asterix24/svaroskey/firmware/svaroskey/hw/hw_sipo.h

/**
 * \file
 * <!--
 * This file is part of BeRTOS.
 *
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
 * As a special exception, you may use this file as part of a free software
 * library without restriction.  Specifically, if other files instantiate
 * templates or use macros or inline functions from this file, or you compile
 * this file and link it with other files to produce an executable, this
 * file does not by itself cause the resulting executable to be covered by
 * the GNU General Public License.  This exception does not however
 * invalidate any other reasons why the executable file might be covered by
 * the GNU General Public License.
 *
 * Copyright 2003, 2004, 2006, 2008, 2009 Develer S.r.l. (http://www.develer.com/)
 * Copyright 2000 Bernie Innocenti <bernie@codewiz.org>
 * All Rights Reserved.
 * -->
 *
 * \brief Macro for HW_SIPO_H
 *
 *
 *
 * \author Andrea Grandi <andrea@develer.com>
 * \author Daniele Basile <asterix@develer.com>
 */

#ifndef HW_SIPO_H
#define HW_SIPO_H

#include <io/stm32.h>

#include <drv/gpio_stm32.h>
#include <drv/clock_stm32.h>

#define SIPO_BASE_SR	((struct stm32_gpio *)GPIOA_BASE)
#define SIPO_BASE_EN	((struct stm32_gpio *)GPIOC_BASE)

#define SI_PIN     BV(13)
#define CLK_PIN    BV(15)
#define LOAD_PIN   BV(14)
#define EN_PIN     (BV(14) | BV(15))

/**
 * Map sipo connection on board.
 */
typedef enum SipoMap
{
	SIPO_CNT
} SipoMap;

/**
 * Define generic macro to set pins logic level
 */
#define SIPO_SET_LEVEL_LOW(dev)   do { (void)dev; } while (0)
#define SIPO_SET_LEVEL_HIGH(dev)  do { (void)dev; } while (0)


/**
 * Generate one low pulse on select line.
 */
#define PULSE_LOW(dev)   do { (void)dev; } while (0)

/**
 * Generate one hight pulse on select line.
 */
#define PULSE_HIGH(dev)  do { (void)dev; } while (0)


/**
 * Define the procedure to drive serial input in sipo device (SI).
 */
#define SIPO_SI_HIGH()                                \
	do {                                              \
		stm32_gpioPinWrite(SIPO_BASE_SR, SI_PIN, true);  \
	} while (0)

#define SIPO_SI_LOW()                                 \
	do {                                              \
		stm32_gpioPinWrite(SIPO_BASE_SR, SI_PIN, false); \
	} while (0)

/**
 * Drive clock to shift SI data into latch.
 */
#define SIPO_SI_CLOCK(clk_pol)                         \
	do {                                               \
		(void)clk_pol;                                 \
		stm32_gpioPinWrite(SIPO_BASE_SR, CLK_PIN, true);  \
		NOP; NOP; NOP; NOP;                            \
		stm32_gpioPinWrite(SIPO_BASE_SR, CLK_PIN, false); \
	} while (0)

/**
 * Do everything needed in order to load dato into sipo.
 */
#define SIPO_LOAD(device, load_pol)                     \
 	do {                                                \
		stm32_gpioPinWrite(SIPO_BASE_SR, LOAD_PIN, true);  \
		NOP; NOP; NOP; NOP;                             \
		stm32_gpioPinWrite(SIPO_BASE_SR, LOAD_PIN, false); \
	} while (0)

/**
 * Enable the shift register output.
 */
#define SIPO_ENABLE()                                  \
	do {                                               \
		stm32_gpioPinWrite(SIPO_BASE_EN, EN_PIN, false);  \
	} while (0)

/**
 * Set polarity for Load, Clk, SI signals.
 */
#define SIPO_SET_LD_LEVEL(device, load_pol)              \
	do {                                                 \
		stm32_gpioPinWrite(SIPO_BASE_SR, LOAD_PIN, false);  \
	} while (0)

#define SIPO_SET_CLK_LEVEL(clock_pol)                    \
	do {                                                 \
		stm32_gpioPinWrite(SIPO_BASE_SR, CLK_PIN, false);   \
	} while (0)

#define SIPO_SET_SI_LEVEL()  do {  SIPO_SI_LOW();  } while (0)

/**
 * Do anything that needed to init sipo pins.
 */
#define SIPO_INIT_PIN() \
	do { \
		/* Enable clocking on GPIOC */ \
		RCC->APB2ENR |= RCC_APB2_GPIOA | RCC_APB2_GPIOC; \
		/* Configure pins as GPIO */ \
		stm32_gpioPinConfig(SIPO_BASE_SR, SI_PIN | CLK_PIN | LOAD_PIN, GPIO_MODE_OUT_PP, GPIO_SPEED_50MHZ); \
		stm32_gpioPinConfig(SIPO_BASE_EN, EN_PIN, GPIO_MODE_OUT_PP, GPIO_SPEED_50MHZ); \
		stm32_gpioPinWrite(SIPO_BASE_SR, SI_PIN | CLK_PIN | LOAD_PIN, true); \
		stm32_gpioPinWrite(SIPO_BASE_EN, EN_PIN, true); \
	} while (0)

#endif /* HW_SIPO_H */
